mulcmu/Modernize-Harmony-880/pcb/alpha/front.png

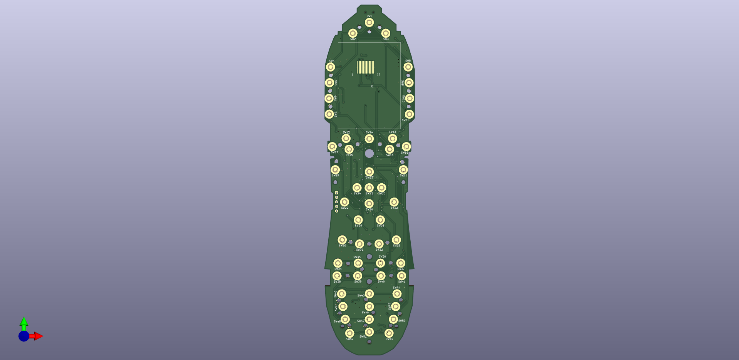
pcb/alpha/front.png
