mulcmu/Modernize-Harmony-880/msp430/src/main.h

#pragma once

#include <msp430.h>
#include <msp430g2553.h>
#include <stdint.h>
#include <Arduino.h>

// Macros for bitwise operations
#define BitSet(arg, bits) ((arg) |= (bits))
#define BitClear(arg, bits) ((arg) &= ~(bits))
#define BitFlip(arg, bits) ((arg) ^= (bits))
#define BitTest(arg, bits) ((arg) & (bits))

EXTERN unsigned long last_button_scan;
EXTERN unsigned long last_button_press;

EXTERN uint16_t counter;
