mulcmu/Modernize-Harmony-880/esp32/800_plus/screens.h

#ifndef EEZ_LVGL_UI_SCREENS_H
#define EEZ_LVGL_UI_SCREENS_H

#include <lvgl.h>
#include <string.h>

#ifdef __cplusplus
extern "C" {
#endif

typedef struct _objects_t {
    lv_obj_t *main;
    lv_obj_t *obj0;
} objects_t;

extern objects_t objects;

extern char button_value[10];

enum ScreensEnum {
    SCREEN_ID_MAIN = 1,
};

void create_screen_main();
void tick_screen_main();

void create_screens();
void tick_screen(int screen_index);


#ifdef __cplusplus
}
#endif

#endif /*EEZ_LVGL_UI_SCREENS_H*/
