mulcmu/Modernize-Harmony-880/esp32/800_plus/tft_setup.h

//Configuration for tft_espi user_setup.h
#define ST7789_DRIVER  
#define TFT_RGB_ORDER TFT_BGR
#define TFT_WIDTH  240
#define TFT_HEIGHT 320 
#define TFT_MOSI            10
#define TFT_SCLK            11
#define TFT_CS              12
#define TFT_DC              13
#define TFT_RST             9
#define TFT_INVERSION_ON

#define TFT_SPI_MODE SPI_MODE0
#define USE_HSPI_PORT
