mulcmu/Modernize-Harmony-880/esp32/800_plus/screens.c

#include "screens.h"
#include "images.h"
#include "fonts.h"
#include "actions.h"
#include "vars.h"
#include "styles.h"
#include "ui.h"

objects_t objects;
lv_obj_t *tick_value_change_obj;

void create_screen_main() {
    lv_obj_t *obj = lv_obj_create(0);
    objects.main = obj;
    lv_obj_set_pos(obj, 0, 0);
    lv_obj_set_size(obj, 240, 320);
    lv_obj_clear_flag(obj, LV_OBJ_FLAG_SCROLLABLE);
    lv_obj_set_style_text_color(obj, lv_color_hex(0xff000000), LV_PART_MAIN | LV_STATE_DEFAULT);
    lv_obj_set_style_text_align(obj, LV_TEXT_ALIGN_CENTER, LV_PART_MAIN | LV_STATE_DEFAULT);
    {
        lv_obj_t *parent_obj = obj;
        {
            lv_obj_t *obj = lv_label_create(parent_obj);
            objects.obj0 = obj;
            lv_obj_set_pos(obj, 0, -1);
            lv_obj_set_size(obj, LV_SIZE_CONTENT, LV_SIZE_CONTENT);
            lv_label_set_text(obj, "");
            lv_obj_set_style_text_font(obj, &lv_font_montserrat_40, LV_PART_MAIN | LV_STATE_DEFAULT);
            lv_obj_set_style_align(obj, LV_ALIGN_CENTER, LV_PART_MAIN | LV_STATE_DEFAULT);
        }
    }
}

void tick_screen_main() {
    {
        const char *new_val = button_value;
        const char *cur_val = lv_label_get_text(objects.obj0);
        if (strcmp(new_val, cur_val) != 0) {
            tick_value_change_obj = objects.obj0;
            lv_label_set_text(objects.obj0, new_val);
            tick_value_change_obj = NULL;
        }
    }
}


void create_screens() {
    lv_disp_t *dispp = lv_disp_get_default();
    lv_theme_t *theme = lv_theme_default_init(dispp, lv_palette_main(LV_PALETTE_BLUE), lv_palette_main(LV_PALETTE_RED), false, LV_FONT_DEFAULT);
    lv_disp_set_theme(dispp, theme);
    
    create_screen_main();
}

typedef void (*tick_screen_func_t)();

tick_screen_func_t tick_screen_funcs[] = {
    tick_screen_main,
};

void tick_screen(int screen_index) {
    tick_screen_funcs[screen_index]();
}
