mulcmu/Modernize-Harmony-880/esp32/800_plus/vars.h

#ifndef EEZ_LVGL_UI_VARS_H
#define EEZ_LVGL_UI_VARS_H

#include <stdint.h>

extern const char *get_var_lv_btn_press();
extern void set_var_lv_btn_press(const char *value);



#endif /*EEZ_LVGL_UI_VARS_H*/
